Circuit-Digest/SmartTape/Core/Inc/vl53lx_platform_user_data.h

/* 
* This file is part of VL53LX Platform
* 
* Copyright (c) 2016, STMicroelectronics - All Rights Reserved 
* 
* License terms: BSD 3-clause "New" or "Revised" License. 
* 
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
* 3. Neither the name of the copyright holder nor the names of its contributors 
* may be used to endorse or promote products derived from this software 
* without specific prior written permission. 
* 
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
*/




#include "stm32g4xx_hal.h"

























#ifndef _VL53LX_PLATFORM_USER_DATA_H_
#define _VL53LX_PLATFORM_USER_DATA_H_

#ifndef __KERNEL__
#include <stdlib.h>
#endif

#include "vl53lx_def.h"

#ifdef __cplusplus
extern "C"
{
#endif


typedef struct {
	VL53LX_DevData_t   Data;
	/*!< Low Level Driver data structure */
    uint8_t   i2c_slave_address;
	uint8_t   comms_type;
	uint16_t  comms_speed_khz;
	I2C_HandleTypeDef *I2cHandle;
	uint8_t   I2cDevAddr;
	int     Present;
	int 	Enabled;
	int LoopState;
	int FirstStreamCountZero;
	int 	Idle;
	int		Ready;
	uint8_t RangeStatus;
	FixPoint1616_t SignalRateRtnMegaCps;
	VL53LX_DeviceState   device_state;  /*!< Device State */
} VL53LX_Dev_t;






typedef VL53LX_Dev_t* VL53LX_DEV;





/**
 * @def VL53LXDevDataGet
 * @brief Get ST private structure @a VL53LX_DevData_t data access
 *
 * @param Dev       Device Handle
 * @param field     ST structure field name
 * It maybe used and as real data "ref" not just as "get" for sub-structure item
 * like VL53L1DevDataGet(FilterData.field)[i] or
 * VL53L1DevDataGet(FilterData.MeasurementIndex)++
 */
#define VL53LXDevDataGet(Dev, field) (Dev->Data.field)


/**
 * @def VL53LXDevDataSet(Dev, field, data)
 * @brief  Set ST private structure @a VL53LX_DevData_t data field
 * @param Dev       Device Handle
 * @param field     ST structure field name
 * @param data      Data to be set
 */
#define VL53LXDevDataSet(Dev, field, data) ((Dev->Data.field) = (data))











#define PALDevDataGet(Dev, field) (Dev->Data.field)












#define PALDevDataSet(Dev, field, VL53LX_PRM_00005) (Dev->Data.field)=(VL53LX_PRM_00005)









#define VL53LXDevStructGetLLDriverHandle(Dev) (&Dev->Data.LLData)








#define VL53LXDevStructGetLLResultsHandle(Dev) (&Dev->Data.llresults)



#ifdef __cplusplus
}
#endif

#endif
