Circuit-Digest/SmartTape/Digi-Tape Tool.ioc

Mcu.UserName=STM32G491CEUx
PA11.Signal=USB_DM
PA12.Signal=USB_DP
PA13.Signal=SYS_JTMS-SWDIO
PA14.Signal=SYS_JTCK-SWCLK
PA15.Signal=I2C1_SCL
PA4.Signal=GPIO_Output
PA5.Signal=SPI1_SCK
PA6.Signal=SPI1_MISO
PA7.Signal=SPI1_MOSI
PA8.Signal=I2C2_SDA
PA9.Signal=I2C2_SCL
PB1.Signal=ADC3_IN1
PB10.Signal=USART3_TX
PB11.Signal=USART3_RX
PB12.Signal=GPIO_Input
PB13.Signal=GPIO_Input
PB7.Signal=I2C1_SDA
PC10.Signal=GPIO_Input
PC11.Signal=GPIO_Output
PF0-OSC_IN.Signal=RCC_OSC_IN
PF1-OSC_OUT.Signal=RCC_OSC_OUT
